danslovich/5DOF_Robot_Arm/Fusion/STLs/shoulder_1.stl

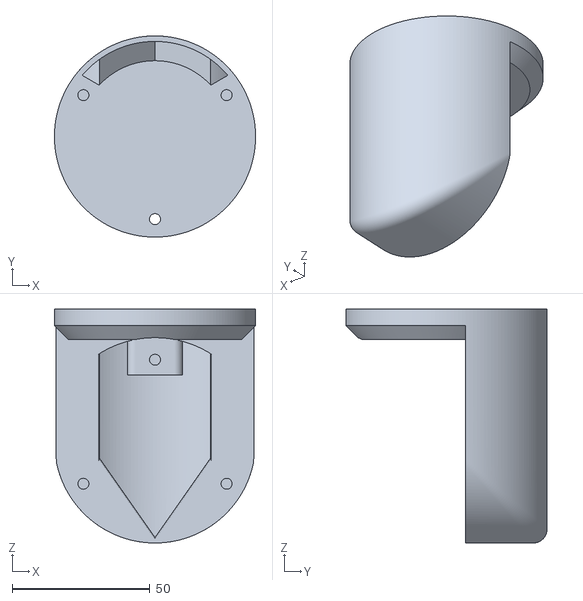
[picture p15: CAD file, 2021-05-07]
Fusion/STLs/shoulder_1.stl
73.0 x 73.0 x 84.9
