danslovich/5DOF_Robot_Arm/Fusion/STLs/drive_plate.stl

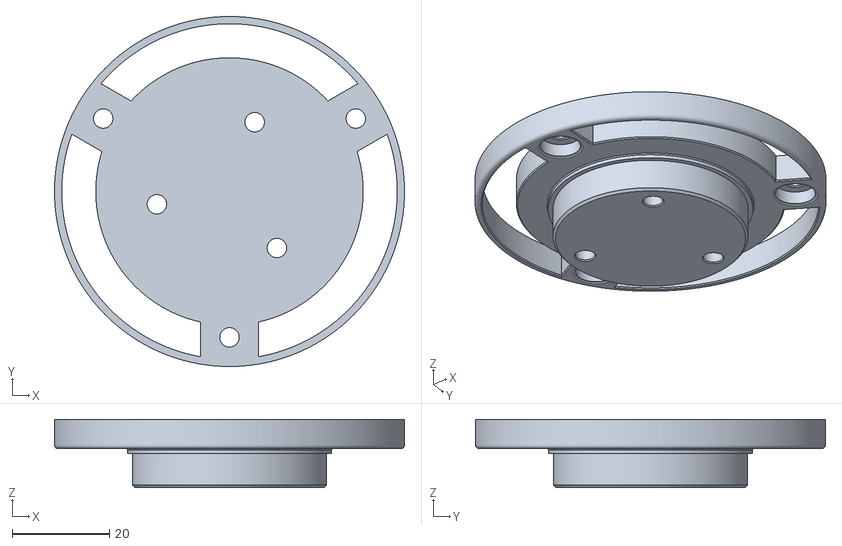
[picture p16: CAD file, 2021-05-07]
Fusion/STLs/drive_plate.stl
72.0 x 72.0 x 14.0
