danslovich/5DOF_Robot_Arm/Fusion/STLs/elbow_1.stl

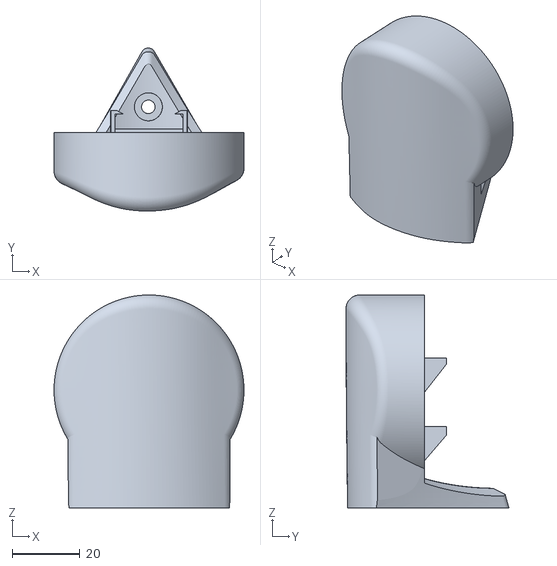
[picture p17: CAD file, 2021-05-07]
Fusion/STLs/elbow_1.stl
56.0 x 48.1 x 62.8
